tomcombriat/TES_10-knobs-synth/10knobs_mono_24bits_MCP4822/hardware/10knobs.sch

## KiCad design 10knobs_mono_24bits_MCP4822/hardware/10knobs.sch (2020-12-10)

Schematic: 10knobs.sch

Parts:
C1: 100m_chem; CP_Radial_D5.0mm_P2.50mm
C2, C7: 0.1m ceram; C_Disc_D3.0mm_W2.0mm_P2.50mm
C4, C5: 10m; CP_Radial_D5.0mm_P2.50mm
C6: 100m chem; CP_Radial_D5.0mm_P2.50mm
D1: 1N914; D_DO-35_SOD27_P7.62mm_Horizontal
D2: LED; LED_D3.0mm
J1: Conn_01x06_Female; PinHeader_1x06_P2.54mm_Vertical
R1: 10; R_Axial_DIN0207_L6.3mm_D2.5mm_P7.62mm_Horizontal
R2, R3, R4, R5: 220; R_Axial_DIN0207_L6.3mm_D2.5mm_P7.62mm_Horizontal
R6: 470k; R_Axial_DIN0207_L6.3mm_D2.5mm_P7.62mm_Horizontal
R7: 33; R_Axial_DIN0207_L6.3mm_D2.5mm_P7.62mm_Horizontal
R8: 1k; R_Axial_DIN0207_L6.3mm_D2.5mm_P7.62mm_Horizontal
R9: 100R; R_Axial_DIN0207_L6.3mm_D2.5mm_P7.62mm_Horizontal
R10, R11: 22k; R_Axial_DIN0207_L6.3mm_D2.5mm_P7.62mm_Horizontal
RV1, RV2, RV3, RV4, RV5, RV6, RV7, RV8, RV10, RV11: 10K; Potentiometer_Alps_RK09K_Single_Vertical
RV9: 1k_Trim; Potentiometer_Bourns_3266Y_Vertical
TP1: T4; TestPoint_THTPad_2.5x2.5mm_Drill1.2mm
TP2: T2; TestPoint_THTPad_2.5x2.5mm_Drill1.2mm
TP3: T5; TestPoint_THTPad_2.5x2.5mm_Drill1.2mm
TP4: IN5; TestPoint_THTPad_2.5x2.5mm_Drill1.2mm
TP5: IN4; TestPoint_THTPad_2.5x2.5mm_Drill1.2mm
TP7: out1; TestPoint_THTPad_2.5x2.5mm_Drill1.2mm
TP9: Batt+; TestPoint_THTPad_2.5x2.5mm_Drill1.2mm
TP10: Batt-; TestPoint_THTPad_2.5x2.5mm_Drill1.2mm
TP11: GND; TestPoint_THTPad_2.5x2.5mm_Drill1.2mm
U1: MCP4822; DIP-8_W7.62mm
U2: BluePill_STM32F103C
U3: 6N138; DIP-8_W7.62mm
U4: LM358; DIP-8_W7.62mm
