tomcombriat/TES_10-knobs-synth/10knobs_mono_16bits_PT8211/softwares/XORAND_mk3/oscil_declaration.h

#ifndef _osc_dec_
#define _osc_dec_


#define POLYPHONY 10



//////////////////////////////////////
////// SQUARE TABLES

#include<tables/BandLimited_SQUARE/512/square_max_75_at_16384_512_int8.h>
#include<tables/BandLimited_SQUARE/512/square_max_81_at_16384_512_int8.h>
#include<tables/BandLimited_SQUARE/512/square_max_88_at_16384_512_int8.h>
#include<tables/BandLimited_SQUARE/512/square_max_96_at_16384_512_int8.h>
#include<tables/BandLimited_SQUARE/512/square_max_106_at_16384_512_int8.h>
#include<tables/BandLimited_SQUARE/512/square_max_118_at_16384_512_int8.h>
#include<tables/BandLimited_SQUARE/512/square_max_134_at_16384_512_int8.h>
#include<tables/BandLimited_SQUARE/512/square_max_154_at_16384_512_int8.h>
#include<tables/BandLimited_SQUARE/512/square_max_182_at_16384_512_int8.h>
#include<tables/BandLimited_SQUARE/512/square_max_221_at_16384_512_int8.h>
#include<tables/BandLimited_SQUARE/512/square_max_282_at_16384_512_int8.h>
#include<tables/BandLimited_SQUARE/512/square_max_356_at_16384_512_int8.h>
#include<tables/BandLimited_SQUARE/512/square_max_431_at_16384_512_int8.h>
#include<tables/BandLimited_SQUARE/512/square_max_546_at_16384_512_int8.h>
#include<tables/BandLimited_SQUARE/512/square_max_630_at_16384_512_int8.h>
#include<tables/BandLimited_SQUARE/512/square_max_744_at_16384_512_int8.h>
#include<tables/BandLimited_SQUARE/512/square_max_910_at_16384_512_int8.h>
#include<tables/BandLimited_SQUARE/512/square_max_1170_at_16384_512_int8.h>
#include<tables/BandLimited_SQUARE/512/square_max_1638_at_16384_512_int8.h>
#include<tables/BandLimited_SQUARE/512/square_max_2730_at_16384_512_int8.h>
#include<tables/BandLimited_SQUARE/512/square_max_8192_at_16384_512_int8.h>    //21

Oscil<SQUARE_MAX_75_AT_16384_512_NUM_CELLS, AUDIO_RATE> aSq75[POLYPHONY] = Oscil<SQUARE_MAX_75_AT_16384_512_NUM_CELLS, AUDIO_RATE> (SQUARE_MAX_75_AT_16384_512_DATA);
Oscil<SQUARE_MAX_75_AT_16384_512_NUM_CELLS, AUDIO_RATE> aSq81[POLYPHONY] = Oscil<SQUARE_MAX_75_AT_16384_512_NUM_CELLS, AUDIO_RATE> (SQUARE_MAX_81_AT_16384_512_DATA);
Oscil<SQUARE_MAX_75_AT_16384_512_NUM_CELLS, AUDIO_RATE> aSq88[POLYPHONY] = Oscil<SQUARE_MAX_75_AT_16384_512_NUM_CELLS, AUDIO_RATE> (SQUARE_MAX_88_AT_16384_512_DATA);
Oscil<SQUARE_MAX_75_AT_16384_512_NUM_CELLS, AUDIO_RATE> aSq96[POLYPHONY] = Oscil<SQUARE_MAX_75_AT_16384_512_NUM_CELLS, AUDIO_RATE> (SQUARE_MAX_96_AT_16384_512_DATA);
Oscil<SQUARE_MAX_75_AT_16384_512_NUM_CELLS, AUDIO_RATE> aSq106[POLYPHONY] = Oscil<SQUARE_MAX_75_AT_16384_512_NUM_CELLS, AUDIO_RATE> (SQUARE_MAX_106_AT_16384_512_DATA);
Oscil<SQUARE_MAX_75_AT_16384_512_NUM_CELLS, AUDIO_RATE> aSq118[POLYPHONY] = Oscil<SQUARE_MAX_75_AT_16384_512_NUM_CELLS, AUDIO_RATE> (SQUARE_MAX_118_AT_16384_512_DATA);
Oscil<SQUARE_MAX_75_AT_16384_512_NUM_CELLS, AUDIO_RATE> aSq134[POLYPHONY] = Oscil<SQUARE_MAX_75_AT_16384_512_NUM_CELLS, AUDIO_RATE> (SQUARE_MAX_134_AT_16384_512_DATA);
Oscil<SQUARE_MAX_75_AT_16384_512_NUM_CELLS, AUDIO_RATE> aSq154[POLYPHONY] = Oscil<SQUARE_MAX_75_AT_16384_512_NUM_CELLS, AUDIO_RATE> (SQUARE_MAX_154_AT_16384_512_DATA);
Oscil<SQUARE_MAX_75_AT_16384_512_NUM_CELLS, AUDIO_RATE> aSq182[POLYPHONY] = Oscil<SQUARE_MAX_75_AT_16384_512_NUM_CELLS, AUDIO_RATE> (SQUARE_MAX_182_AT_16384_512_DATA);
Oscil<SQUARE_MAX_75_AT_16384_512_NUM_CELLS, AUDIO_RATE> aSq221[POLYPHONY] = Oscil<SQUARE_MAX_75_AT_16384_512_NUM_CELLS, AUDIO_RATE> (SQUARE_MAX_221_AT_16384_512_DATA);
Oscil<SQUARE_MAX_75_AT_16384_512_NUM_CELLS, AUDIO_RATE> aSq282[POLYPHONY] = Oscil<SQUARE_MAX_75_AT_16384_512_NUM_CELLS, AUDIO_RATE> (SQUARE_MAX_282_AT_16384_512_DATA);
Oscil<SQUARE_MAX_75_AT_16384_512_NUM_CELLS, AUDIO_RATE> aSq356[POLYPHONY] = Oscil<SQUARE_MAX_75_AT_16384_512_NUM_CELLS, AUDIO_RATE> (SQUARE_MAX_356_AT_16384_512_DATA);
Oscil<SQUARE_MAX_75_AT_16384_512_NUM_CELLS, AUDIO_RATE> aSq431[POLYPHONY] = Oscil<SQUARE_MAX_75_AT_16384_512_NUM_CELLS, AUDIO_RATE> (SQUARE_MAX_431_AT_16384_512_DATA);
Oscil<SQUARE_MAX_75_AT_16384_512_NUM_CELLS, AUDIO_RATE> aSq546[POLYPHONY] = Oscil<SQUARE_MAX_75_AT_16384_512_NUM_CELLS, AUDIO_RATE> (SQUARE_MAX_546_AT_16384_512_DATA);
Oscil<SQUARE_MAX_75_AT_16384_512_NUM_CELLS, AUDIO_RATE> aSq630[POLYPHONY] = Oscil<SQUARE_MAX_75_AT_16384_512_NUM_CELLS, AUDIO_RATE> (SQUARE_MAX_630_AT_16384_512_DATA);
Oscil<SQUARE_MAX_75_AT_16384_512_NUM_CELLS, AUDIO_RATE> aSq744[POLYPHONY] = Oscil<SQUARE_MAX_75_AT_16384_512_NUM_CELLS, AUDIO_RATE> (SQUARE_MAX_744_AT_16384_512_DATA);
Oscil<SQUARE_MAX_75_AT_16384_512_NUM_CELLS, AUDIO_RATE> aSq910[POLYPHONY] = Oscil<SQUARE_MAX_75_AT_16384_512_NUM_CELLS, AUDIO_RATE> (SQUARE_MAX_910_AT_16384_512_DATA);
Oscil<SQUARE_MAX_75_AT_16384_512_NUM_CELLS, AUDIO_RATE> aSq1170[POLYPHONY] = Oscil<SQUARE_MAX_75_AT_16384_512_NUM_CELLS, AUDIO_RATE> (SQUARE_MAX_1170_AT_16384_512_DATA);
Oscil<SQUARE_MAX_75_AT_16384_512_NUM_CELLS, AUDIO_RATE> aSq1638[POLYPHONY] = Oscil<SQUARE_MAX_75_AT_16384_512_NUM_CELLS, AUDIO_RATE> (SQUARE_MAX_1638_AT_16384_512_DATA);
Oscil<SQUARE_MAX_75_AT_16384_512_NUM_CELLS, AUDIO_RATE> aSq2730[POLYPHONY] = Oscil<SQUARE_MAX_75_AT_16384_512_NUM_CELLS, AUDIO_RATE> (SQUARE_MAX_2730_AT_16384_512_DATA);
Oscil<SQUARE_MAX_75_AT_16384_512_NUM_CELLS, AUDIO_RATE> aSq8192[POLYPHONY] = Oscil<SQUARE_MAX_75_AT_16384_512_NUM_CELLS, AUDIO_RATE> (SQUARE_MAX_8192_AT_16384_512_DATA);

MetaOscil<SQUARE_MAX_75_AT_16384_512_NUM_CELLS, AUDIO_RATE,21> aSquare[POLYPHONY];



//////////////////////////////////////
//////////// SAW TABLES

#include<tables/BandLimited_SAW/512/saw_max_154_at_16384_512_int8.h>
#include<tables/BandLimited_SAW/512/saw_max_182_at_16384_512_int8.h>
#include<tables/BandLimited_SAW/512/saw_max_221_at_16384_512_int8.h>
#include<tables/BandLimited_SAW/512/saw_max_282_at_16384_512_int8.h>
#include<tables/BandLimited_SAW/512/saw_max_356_at_16384_512_int8.h>
#include<tables/BandLimited_SAW/512/saw_max_431_at_16384_512_int8.h>
#include<tables/BandLimited_SAW/512/saw_max_546_at_16384_512_int8.h>
#include<tables/BandLimited_SAW/512/saw_max_630_at_16384_512_int8.h>
#include<tables/BandLimited_SAW/512/saw_max_744_at_16384_512_int8.h>
#include<tables/BandLimited_SAW/512/saw_max_910_at_16384_512_int8.h>
#include<tables/BandLimited_SAW/512/saw_max_1170_at_16384_512_int8.h>
#include<tables/BandLimited_SAW/512/saw_max_1638_at_16384_512_int8.h>
#include<tables/BandLimited_SAW/512/saw_max_2730_at_16384_512_int8.h>
#include<tables/BandLimited_SAW/512/saw_max_8192_at_16384_512_int8.h>  //14


Oscil<SAW_MAX_154_AT_16384_512_NUM_CELLS, AUDIO_RATE> aSaw154[POLYPHONY] = Oscil<SAW_MAX_154_AT_16384_512_NUM_CELLS, AUDIO_RATE> (SAW_MAX_154_AT_16384_512_DATA);
Oscil<SAW_MAX_154_AT_16384_512_NUM_CELLS, AUDIO_RATE> aSaw182[POLYPHONY] = Oscil<SAW_MAX_154_AT_16384_512_NUM_CELLS, AUDIO_RATE> (SAW_MAX_182_AT_16384_512_DATA);
Oscil<SAW_MAX_154_AT_16384_512_NUM_CELLS, AUDIO_RATE> aSaw221[POLYPHONY] = Oscil<SAW_MAX_154_AT_16384_512_NUM_CELLS, AUDIO_RATE> (SAW_MAX_221_AT_16384_512_DATA);
Oscil<SAW_MAX_154_AT_16384_512_NUM_CELLS, AUDIO_RATE> aSaw282[POLYPHONY] = Oscil<SAW_MAX_154_AT_16384_512_NUM_CELLS, AUDIO_RATE> (SAW_MAX_282_AT_16384_512_DATA);
Oscil<SAW_MAX_154_AT_16384_512_NUM_CELLS, AUDIO_RATE> aSaw356[POLYPHONY] = Oscil<SAW_MAX_154_AT_16384_512_NUM_CELLS, AUDIO_RATE> (SAW_MAX_356_AT_16384_512_DATA);
Oscil<SAW_MAX_154_AT_16384_512_NUM_CELLS, AUDIO_RATE> aSaw431[POLYPHONY] = Oscil<SAW_MAX_154_AT_16384_512_NUM_CELLS, AUDIO_RATE> (SAW_MAX_431_AT_16384_512_DATA);
Oscil<SAW_MAX_154_AT_16384_512_NUM_CELLS, AUDIO_RATE> aSaw546[POLYPHONY] = Oscil<SAW_MAX_154_AT_16384_512_NUM_CELLS, AUDIO_RATE> (SAW_MAX_546_AT_16384_512_DATA);
Oscil<SAW_MAX_154_AT_16384_512_NUM_CELLS, AUDIO_RATE> aSaw630[POLYPHONY] = Oscil<SAW_MAX_154_AT_16384_512_NUM_CELLS, AUDIO_RATE> (SAW_MAX_630_AT_16384_512_DATA);
Oscil<SAW_MAX_154_AT_16384_512_NUM_CELLS, AUDIO_RATE> aSaw744[POLYPHONY] = Oscil<SAW_MAX_154_AT_16384_512_NUM_CELLS, AUDIO_RATE> (SAW_MAX_744_AT_16384_512_DATA);
Oscil<SAW_MAX_154_AT_16384_512_NUM_CELLS, AUDIO_RATE> aSaw910[POLYPHONY] = Oscil<SAW_MAX_154_AT_16384_512_NUM_CELLS, AUDIO_RATE> (SAW_MAX_910_AT_16384_512_DATA);
Oscil<SAW_MAX_154_AT_16384_512_NUM_CELLS, AUDIO_RATE> aSaw1170[POLYPHONY] = Oscil<SAW_MAX_154_AT_16384_512_NUM_CELLS, AUDIO_RATE> (SAW_MAX_1170_AT_16384_512_DATA);
Oscil<SAW_MAX_154_AT_16384_512_NUM_CELLS, AUDIO_RATE> aSaw1638[POLYPHONY] = Oscil<SAW_MAX_154_AT_16384_512_NUM_CELLS, AUDIO_RATE> (SAW_MAX_1638_AT_16384_512_DATA);
Oscil<SAW_MAX_154_AT_16384_512_NUM_CELLS, AUDIO_RATE> aSaw2730[POLYPHONY] = Oscil<SAW_MAX_154_AT_16384_512_NUM_CELLS, AUDIO_RATE> (SAW_MAX_2730_AT_16384_512_DATA);
Oscil<SAW_MAX_154_AT_16384_512_NUM_CELLS, AUDIO_RATE> aSaw8192[POLYPHONY] = Oscil<SAW_MAX_154_AT_16384_512_NUM_CELLS, AUDIO_RATE> (SAW_MAX_8192_AT_16384_512_DATA);

MetaOscil<SAW_MAX_154_AT_16384_512_NUM_CELLS, AUDIO_RATE,14> aSaw[POLYPHONY];

/////////////////////////////////////
////////////////////// TRI

#include <tables/triangle2048_int8.h>

#include<tables/BandLimited_TRI/512/tri_max_106_at_16384_512_int8.h>
#include<tables/BandLimited_TRI/512/tri_max_118_at_16384_512_int8.h>
#include<tables/BandLimited_TRI/512/tri_max_134_at_16384_512_int8.h>
#include<tables/BandLimited_TRI/512/tri_max_154_at_16384_512_int8.h>
#include<tables/BandLimited_TRI/512/tri_max_182_at_16384_512_int8.h>
#include<tables/BandLimited_TRI/512/tri_max_221_at_16384_512_int8.h>
#include<tables/BandLimited_TRI/512/tri_max_282_at_16384_512_int8.h>
#include<tables/BandLimited_TRI/512/tri_max_356_at_16384_512_int8.h>
#include<tables/BandLimited_TRI/512/tri_max_431_at_16384_512_int8.h>
#include<tables/BandLimited_TRI/512/tri_max_546_at_16384_512_int8.h>
#include<tables/BandLimited_TRI/512/tri_max_630_at_16384_512_int8.h>
#include<tables/BandLimited_TRI/512/tri_max_744_at_16384_512_int8.h>
#include<tables/BandLimited_TRI/512/tri_max_910_at_16384_512_int8.h>
#include<tables/BandLimited_TRI/512/tri_max_1170_at_16384_512_int8.h>
#include<tables/BandLimited_TRI/512/tri_max_1638_at_16384_512_int8.h>
#include<tables/BandLimited_TRI/512/tri_max_2730_at_16384_512_int8.h>
#include<tables/BandLimited_TRI/512/tri_max_8192_at_16384_512_int8.h>    //17


Oscil<TRI_MAX_106_AT_16384_512_NUM_CELLS, AUDIO_RATE> aTri106[POLYPHONY] = Oscil<TRI_MAX_106_AT_16384_512_NUM_CELLS, AUDIO_RATE> (TRI_MAX_106_AT_16384_512_DATA);
Oscil<TRI_MAX_106_AT_16384_512_NUM_CELLS, AUDIO_RATE> aTri118[POLYPHONY] = Oscil<TRI_MAX_106_AT_16384_512_NUM_CELLS, AUDIO_RATE> (TRI_MAX_118_AT_16384_512_DATA);
Oscil<TRI_MAX_106_AT_16384_512_NUM_CELLS, AUDIO_RATE> aTri134[POLYPHONY] = Oscil<TRI_MAX_106_AT_16384_512_NUM_CELLS, AUDIO_RATE> (TRI_MAX_134_AT_16384_512_DATA);
Oscil<TRI_MAX_106_AT_16384_512_NUM_CELLS, AUDIO_RATE> aTri154[POLYPHONY] = Oscil<TRI_MAX_106_AT_16384_512_NUM_CELLS, AUDIO_RATE> (TRI_MAX_154_AT_16384_512_DATA);
Oscil<TRI_MAX_106_AT_16384_512_NUM_CELLS, AUDIO_RATE> aTri182[POLYPHONY] = Oscil<TRI_MAX_106_AT_16384_512_NUM_CELLS, AUDIO_RATE> (TRI_MAX_182_AT_16384_512_DATA);
Oscil<TRI_MAX_106_AT_16384_512_NUM_CELLS, AUDIO_RATE> aTri221[POLYPHONY] = Oscil<TRI_MAX_106_AT_16384_512_NUM_CELLS, AUDIO_RATE> (TRI_MAX_221_AT_16384_512_DATA);
Oscil<TRI_MAX_106_AT_16384_512_NUM_CELLS, AUDIO_RATE> aTri282[POLYPHONY] = Oscil<TRI_MAX_106_AT_16384_512_NUM_CELLS, AUDIO_RATE> (TRI_MAX_282_AT_16384_512_DATA);
Oscil<TRI_MAX_106_AT_16384_512_NUM_CELLS, AUDIO_RATE> aTri356[POLYPHONY] = Oscil<TRI_MAX_106_AT_16384_512_NUM_CELLS, AUDIO_RATE> (TRI_MAX_356_AT_16384_512_DATA);
Oscil<TRI_MAX_106_AT_16384_512_NUM_CELLS, AUDIO_RATE> aTri431[POLYPHONY] = Oscil<TRI_MAX_106_AT_16384_512_NUM_CELLS, AUDIO_RATE> (TRI_MAX_431_AT_16384_512_DATA);
Oscil<TRI_MAX_106_AT_16384_512_NUM_CELLS, AUDIO_RATE> aTri546[POLYPHONY] = Oscil<TRI_MAX_106_AT_16384_512_NUM_CELLS, AUDIO_RATE> (TRI_MAX_546_AT_16384_512_DATA);
Oscil<TRI_MAX_106_AT_16384_512_NUM_CELLS, AUDIO_RATE> aTri630[POLYPHONY] = Oscil<TRI_MAX_106_AT_16384_512_NUM_CELLS, AUDIO_RATE> (TRI_MAX_630_AT_16384_512_DATA);
Oscil<TRI_MAX_106_AT_16384_512_NUM_CELLS, AUDIO_RATE> aTri744[POLYPHONY] = Oscil<TRI_MAX_106_AT_16384_512_NUM_CELLS, AUDIO_RATE> (TRI_MAX_744_AT_16384_512_DATA);
Oscil<TRI_MAX_106_AT_16384_512_NUM_CELLS, AUDIO_RATE> aTri910[POLYPHONY] = Oscil<TRI_MAX_106_AT_16384_512_NUM_CELLS, AUDIO_RATE> (TRI_MAX_910_AT_16384_512_DATA);
Oscil<TRI_MAX_106_AT_16384_512_NUM_CELLS, AUDIO_RATE> aTri1170[POLYPHONY] = Oscil<TRI_MAX_106_AT_16384_512_NUM_CELLS, AUDIO_RATE> (TRI_MAX_1170_AT_16384_512_DATA);
Oscil<TRI_MAX_106_AT_16384_512_NUM_CELLS, AUDIO_RATE> aTri1638[POLYPHONY] = Oscil<TRI_MAX_106_AT_16384_512_NUM_CELLS, AUDIO_RATE> (TRI_MAX_1638_AT_16384_512_DATA);
Oscil<TRI_MAX_106_AT_16384_512_NUM_CELLS, AUDIO_RATE> aTri2730[POLYPHONY] = Oscil<TRI_MAX_106_AT_16384_512_NUM_CELLS, AUDIO_RATE> (TRI_MAX_2730_AT_16384_512_DATA);
Oscil<TRI_MAX_106_AT_16384_512_NUM_CELLS, AUDIO_RATE> aTri8192[POLYPHONY] = Oscil<TRI_MAX_106_AT_16384_512_NUM_CELLS, AUDIO_RATE> (TRI_MAX_8192_AT_16384_512_DATA);


MetaOscil<TRI_MAX_106_AT_16384_512_NUM_CELLS, AUDIO_RATE, 17> aTri[POLYPHONY];

/////////////////////////////////////
///////////////////// COS


#include <tables/cos2048_int8.h>
#include <tables/cos512_int8.h>





#endif
