tomcombriat/TES_10-knobs-synth/10knobs_mono_16bits_PT8211/softwares/DIGITAL_SENAP_sax/midi_handles.h

#ifndef _midi_handles_
#define _midi_handles_


void HandleNoteOn(byte channel, byte note, byte velocity);
void HandleNoteOff(byte channel, byte note, byte velocity);
void HandleControlChange(byte channel, byte control, byte val);
void HandlePitchBend(byte channel, int bend);

#endif
