tomcombriat/TES_10-knobs-synth/10knobs_mono_16bits_PT8211/softwares/DIGITAL_SENAP_sax/dual_type_pot.h

#ifndef _DTP_
#define _DTP_

// For the mod on carrier ratio: half the course give an integer value, the remaining a full continuum


int inline dual_type_pot(int input)
{
  if (input <= 2048) return (input >> 7) << 7;
  else return (input - 2048);

}

#endif
